373dp3/WiFi-Arduino-Barcode-experimental-/client/Esp8266BarcodeReader/TableViewManager.cpp

// 
// 
// 

#include "TableViewManager.h"


TableViewWrapper::TableViewWrapper(CommonController * pBackController)
{
	char * buf = (char*)malloc(JSON_BUFFER_SIZE * sizeof(char*));
	getList(buf, JSON_BUFFER_SIZE);
	this->parseResponseJson(buf);
	free(buf);

	this->state = CELL_SELECT;
	this->pBackController = pBackController;

	this->dumpSerial();
	this->updateLcd();
}

TableViewWrapper::TableViewWrapper(char * listInfoJson, CommonController * pBackController)
{
	this->parseResponseJson(listInfoJson);

	this->state = CELL_SELECT;
	this->pBackController = pBackController;

	this->dumpSerial();
	this->updateLcd();
}

TableViewWrapper::~TableViewWrapper()
{
	Dispose();
}

void TableViewWrapper::refreshModel()
{
	D("refreshModel");
	Dispose();

	char * buf = (char*)malloc(JSON_BUFFER_SIZE * sizeof(char*));
	getList(buf, JSON_BUFFER_SIZE);
	this->parseResponseJson(buf);
	free(buf);

	this->dumpSerial();
	D("refreshModel . done");
}

void TableViewWrapper::parseResponseJson(const char * json)
{
	D("parseResponseJson");
	char* JsonCharBuffer = (char*)malloc(this->JSON_BUF_LENGTH);
	memset(JsonCharBuffer, 0, this->JSON_BUF_LENGTH);
	JSONBuffer.clear();
	strcpy(JsonCharBuffer, json);
	JsonObject& parsed = JSONBuffer.parseObject(JsonCharBuffer);
	if (parsed.success()) {
		this->pModel = new TableViewModel(&parsed);
	}
	else {
		D("[ERROR] parse failer.");
		Serial.println(json);
	}
	free(JsonCharBuffer);
	D("parseResponseJson . done");
}

void TableViewWrapper::getList(char* buf, int bufsize, int direction, const char* strId)
{
	Serial.println(F("getList"));

	JSONBuffer.clear();
	JsonObject& JSONencoder = JSONBuffer.createObject();
	if (strId != NULL) {
		JSONencoder["id"] = strId;
		D("id: ", strId);
	}
	JSONencoder["name"] = "";
	JSONencoder["mode"] = "list";
	JSONencoder["dir"] = String(direction);

	this->_postCommon(JSONencoder, buf, bufsize);
	HIDSelector::clearBuffer();

	Serial.println(F("getList . done"));
}

void TableViewWrapper::getOtherPage(int8_t direction)
{
	D("pageFlag:", String(pModel->pageFlag).c_str());
	D("direction:", String(direction).c_str());
	//遷移可能なページがない場合は終了
	if (pModel->pageFlag == 0) {
		D("no tr page");
		return;
	}
	//上(新)方向制約
	if ((direction > 0) && ((pModel->pageFlag & 0x01) == 0)) {
		D("no up(new) page");
		return;
	}
	//下(旧)方向制約
	if ((direction < 0) && ((pModel->pageFlag & 0x02) == 0)) {
		D("no down(old) page");
		return;
	}
	String strId = String(this->pModel->ppRows[posY]->strId);

	Dispose();

	char * buf = (char*)malloc(JSON_BUFFER_SIZE * sizeof(char*));
	getList(buf, JSON_BUFFER_SIZE, direction, strId.c_str());
	this->parseResponseJson(buf);
	free(buf);
	strId.~String();

	//フォーカスするセルの検討
	if (direction > 0) {
		//上(新)方向の場合
		lcdPosY = pModel->rowSize - LCD_SIZE_Y;
		posY = pModel->rowSize - 1;
		if (lcdPosY < 0) { lcdPosY = 0; }
		if (posY < 0) { posY = 0; }
		//D("set lcdPosY:", String(lcdPosY).c_str());
		//D("set posY:", String(posY).c_str());
	}
	if (direction < 0) {
		lcdPosY = 0;
		posY = 0;
	}//下(旧)方向の場合

	D("getOtherPage . done");
}

void TableViewWrapper::postUpdate()
{
	//post実行
	JSONBuffer.clear();
	Serial.println(F("postUpdate"));
	JsonObject& JSONencoder = JSONBuffer.createObject();
	JSONencoder["mode"] = "update";
	JSONencoder["id"] = this->pModel->ppRows[posY]->strId;
	JSONencoder["posX"] = posX;

	this->_postCommon(JSONencoder, NULL, 0);

	HIDSelector::clearBuffer();
	Serial.println(F("postUpdate . done"));
}

void TableViewWrapper::postDelete()
{
	JSONBuffer.clear();
	Serial.println(F("postDelete"));
	JsonObject& JSONencoder = JSONBuffer.createObject();
	JSONencoder["mode"] = "delete";
	JSONencoder["id"] = this->pModel->ppRows[posY]->strId;

	this->_postCommon(JSONencoder, NULL, 0);

	HIDSelector::clearBuffer();
}

void TableViewWrapper::_postCommon(JsonObject & JSONencoder, char * responseBuf, int bufsize)
{
	Serial.println(F("_postCommon"));

	//送信処理
	{
		HTTPClient http;
		String url = net.getBaseURL();
		url += net.session_uri;
		Serial.println(url.c_str());
		http.begin(url.c_str());

		JSONencoder["bc"] = HIDSelector::BARCODE;
		JSONencoder["np"] = HIDSelector::TENKEY;
		JSONencoder["bt"] = net.session_key;
		//JSONencoder["name"] = "";

		uint8_t mac0[6];

#ifdef defined(ESP32)
		esp_efuse_mac_get_default(mac0);
#else 
		WiFi.macAddress(mac0);
#endif

		char macstr[16];
		memset(macstr, 0, sizeof(macstr));
		sprintf(macstr, "%02X%02X%02X%02X%02X%02X", mac0[0], mac0[1], mac0[2], mac0[3], mac0[4], mac0[5]);
		JSONencoder["mac"] = macstr;


		char* JsonCharBuffer = (char*)malloc(JSON_POST_BUFFER_SIZE);
		if (JsonCharBuffer == NULL) {
			Serial.println(F("[ERROR] malloc failed"));
		}
		JSONencoder.printTo(JsonCharBuffer, JSON_POST_BUFFER_SIZE);
		JSONencoder.end();

		Serial.print(F("JSON POST:"));
		Serial.println(JsonCharBuffer);

		bool isOk = false;
		bool isAutoFetch = false;

		while (true) {
			int httpCode = http.POST(JsonCharBuffer);
			if (httpCode > 0) { //Check for the returning code
				String payload = http.getString();
				Serial.print(F("httpCode: "));
				Serial.println(httpCode);
				Serial.print(F("payload: "));
				Serial.println(payload);
				JSONBuffer.clear();

				_printPostResponse(payload, responseBuf, bufsize);

				http.end();
				break;//whileループを抜ける
			}
			else {
				if (Serial.available() > 10) { return; }//設定書き込み指示
				Serial.println(F("Error on HTTP request"));
				lcd.clear();
				lcd.setCursor(0, 0);
				lcd.print(F("ERROR 003"));
				lcd.setCursor(0, 1);
				lcd.print(F("CONN failure"));
				delay(3000);
				http.end();
			}

		}
		free(JsonCharBuffer);

	}//送信処理終わり

	Serial.println(F("_postCommon . done"));

}

void TableViewWrapper::_printPostResponse(String & payload, char * responseBuf, int bufsize)
{
	D("_printPostResponse");
	JsonObject& parsed = JSONBuffer.parseObject(payload);
	lcd.clear();
	switch (state)
	{
	case TableViewWrapper::CELL_SELECT:
		D("_printPostResponse . CELL_SELECT");
		if (parsed.success() && parsed.containsKey("d")) {
			if (payload.length() < bufsize) {
				strcpy(responseBuf, payload.c_str());
			}
			else {
				lcd.print("SIZE OVER");
			}
			beepCheck(&parsed);
		}
		else {
			Serial.println("no contains d");
			lcd.print(payload);
		}
		break;
	case TableViewWrapper::VALUE_EDIT:
		break;
	case TableViewWrapper::ROW_DELETE:
		break;
	default:
		break;
	}
	parsed.end();
	D("_printPostResponse . done");
}


void TableViewWrapper::valueChange()
{
	if (state == CELL_SELECT) {
		switch (HIDSelector::TENKEY[0])
		{
		case '8':// up
			posY--;
			if (posY < 0) {
				//サーバ連携のページ送り処理
				posY = 0;
				getOtherPage(1);//上のほうが時間が新しいので、8はプラス
			}
			else {
				lcdPosY = posY;//lcdの1行目に表示する行番号
			}
			break;
		case '2':// down
			posY++;
			if (posY > this->pModel->rowSize - 1) { 
				//サーバ連携のページ送り処理
				posY = this->pModel->rowSize - 1;
				getOtherPage(-1);//下のほうが時間が古い。2はマイナス
			}
			else {
				lcdPosY = posY - 1;//lcdの1行目に表示する行番号
			}
			if (lcdPosY < 0) { lcdPosY = 0; }
			break;
		case '4':// left
			posX--;
			if (posX < 0) { posX = 0; }
			break;
		case '6':// right
			posX++;
			break;
		default:
			break;
		}
		this->updateLcd();


		memset(HIDSelector::TENKEY, 0, sizeof(HIDSelector::TENKEY));
	}

	if (state == VALUE_EDIT) {
		scr.onChangeTenkey(HIDSelector::TENKEY);
	}

	if(state == ROW_DELETE) {
		switch (HIDSelector::TENKEY[0])
		{
		case '1':// ok
			//サーバへの削除コマンド送信
			Serial.print(F("delete ok, posY:"));
			Serial.println(posY);
			D("id:", this->pModel->ppRows[posY]->strId);
			this->postDelete();

			//画面遷移
			posX = 0; posY = 0; lcdPosY = 0;
			state = CELL_SELECT;
			this->refreshModel();
			this->_updateLcdCELL_SELECT();

			break;
		case '9':// Cancel
			Serial.println(F("delete cancel"));
			state = CELL_SELECT;
			this->updateLcd();
			break;
		default:
			break;
		}

		memset(HIDSelector::TENKEY, 0, sizeof(HIDSelector::TENKEY));
	}

}


void TableViewWrapper::onBarcodeEnter()
{
	if (strcmp(HIDSelector::BARCODE, "RB$%") == 0) {
#ifdef DP3_ESP32
#else
		ESP.reset();
#endif
	}
	if (strcmp(HIDSelector::BARCODE, "HO$%") == 0) {
	}
	//EE$% (Edit End)
	if (strcmp(HIDSelector::BARCODE, "EE$%") == 0) {
		HIDSelector::setCommonController(this->pBackController);
		this->pBackController->resume();
	}
}

void TableViewWrapper::onTenkeyEnter()
{
	if (state == VALUE_EDIT) {
		//サーバへの編集コマンド送信
		Serial.print(F("edit pos:"));
		Serial.print(posX);
		Serial.print(F(", "));
		Serial.print(posY);
		Serial.print(F(" => "));
		Serial.println(HIDSelector::TENKEY);
		D("id:", this->pModel->ppRows[posY]->strId);
		this->postUpdate();
		state = CELL_SELECT;
		this->refreshModel();
		//画面遷移
		this->_updateLcdCELL_SELECT();
	}
	else {
		Serial.print("posX:"); Serial.print(posX);
		Serial.print(" colSize:"); Serial.println(pModel->ppRows[0]->colSize);
		//削除を選択しているか？
		if (posX >= pModel->ppRows[0]->colSize) {
			lcd.clear();
			lcd.setCursor(0, 0);
			//ｻｸｼﾞｮ ｼﾏｽｶ?
			lcd.print(F("\xbb\xb8\xbc\xde\xae\x20\xbc\xcf\xbd\xb6\x3f"));
			lcd.setCursor(0, 1);
			lcd.print(F("OK:1 Cancel:9"));
			state = ROW_DELETE;
		}
		else {
			state = VALUE_EDIT;
			this->_updateLcdVALUE_EDIT();
		}
	}
}

void TableViewWrapper::updateLcd()
{
	if (state == CELL_SELECT) {
		this->_updateLcdCELL_SELECT();
	}
	else {
		this->_updateLcdVALUE_EDIT();
	}
}

void TableViewWrapper::_updateLcdCELL_SELECT()
{
	lcd.clear();
	lcd.setCursor(0, 0);
	if (this->pModel == NULL) {
		lcd.print(F("No model"));
		return;
	}
	int rowSize = this->pModel->rowSize;
	if (rowSize == 0) {
		lcd.print(F("Row size: 0"));
		return;
	}
	int colSize = this->pModel->ppRows[0]->colSize;
	if (colSize == 0) {
		lcd.print(F("Col size: 0"));
		return;
	}

	//配列を超えない事の保証(削除付き)
	if (posX > colSize) { posX = colSize; }

	int printLen = 0;

	Serial.print("use lcdPosY:"); Serial.println(lcdPosY);
	Serial.print("use posY:"); Serial.println(posY);

	//時刻部分の描画
	if (posX == 0) {
		for (int i = lcdPosY; i < lcdPosY + LCD_SIZE_Y; i++) {
			if (i >= pModel->rowSize) { break; }
			lcd.setCursor(0, i - lcdPosY);
			char * val = pModel->ppRows[i]->strHhMm;
			lcd.print(val);
			int tmpLen = strlen(val);
			if (printLen < tmpLen) { printLen = tmpLen; }
		}
	}
	printLen += 1;

	//X方向表示原点の調査
	int printLenOrg = printLen;
	int orgX = 0;
	//Serial.println("--");
	//Serial.print("colSize:"); Serial.println(colSize);
	//Serial.print("posX:"); Serial.println(posX);
	for (int i = 0; i < colSize - orgX + 1/* +1は削除分 */; i++) {
		//Serial.print("	i:"); Serial.println(i);
		int maxLen = 0;
		if (i == colSize - orgX) {
			//削除
			maxLen = DELETE_WORD_LENGTH;
			//Serial.println("append delete_word_length into maxLen.");
		}
		else {
			//通常セル
			for (int j = 0; j < rowSize; j++) {
				int tmpLen = strlen(pModel->ppRows[j]->ppCols[i + orgX]);
				if (maxLen < tmpLen) { maxLen = tmpLen; }
			}
		}
		printLen += maxLen + 1;
		//超過した場合は、原点を1オフセットして再計算
		//(初回から超過する場合は除外)
		Serial.print("	printLen:"); Serial.println(printLen);
		if ((printLen >= LCD_SIZE_X) && (i > 0)) {
			i = -1;
			printLen = printLenOrg;
			orgX++;
			//Serial.print("size over. inc offset: "); Serial.println(orgX);
		}
		//超過せずにたどり着いた場合は終了
		if (i + orgX == posX) {
			//Serial.println("Break");
			break;
		}
	}
	//Serial.print("orgX: "); Serial.println(orgX);
	printLen = printLenOrg;


	//配列部分の描画
	for (int i = orgX; i < colSize + 1; i++) {
		int maxLen = 0;
		if (i >= colSize) {
			for (int j = 0; j < rowSize; j++) {
				//ｻｸｼﾞｮ
				int tmpLen = DELETE_WORD_LENGTH;//半角カナ5文字
				if (maxLen < tmpLen) { maxLen = tmpLen; }
				//表示範囲外のデータはLCDにコマンドを送らない
				if (j < lcdPosY) { continue; }
				if (j >= lcdPosY + LCD_SIZE_Y) { continue; }
				lcd.setCursor(printLen, j - lcdPosY);
				lcd.print(F("\xbb\xb8\xbc\xde\xae"));
			}
		}
		else {
			for (int j = 0; j < rowSize; j++) {
				char* val = pModel->ppRows[j]->ppCols[i];
				int tmpLen = strlen(val);
				if (maxLen < tmpLen) { maxLen = tmpLen; }
				//表示範囲外のデータはLCDにコマンドを送らない
				if (j < lcdPosY) { continue; }
				if (j >= lcdPosY + LCD_SIZE_Y) { continue; }
				lcd.setCursor(printLen, j - lcdPosY);
				lcd.print(val);
			}
		}

		//カーソルの描画判定
		if (i == posX) {
			lcd.setCursor(printLen - 1, posY - lcdPosY);
			lcd.print("[");
			lcd.setCursor(printLen + maxLen, posY - lcdPosY);
			lcd.print("]");
		}
		printLen += maxLen + 1;

		//表示範囲を超えている場合は'>'で埋める
		if ((printLen >= LCD_SIZE_X) && (i != posX)) {
			char* tmpChar = (char*)malloc(maxLen + 1);
			for (int i = 0; i < maxLen; i++) tmpChar[i] = '>';
			tmpChar[maxLen] = 0x00;
			lcd.setCursor(printLen - maxLen - 1, 0);
			lcd.print(tmpChar);
			if (pModel->rowSize > 1) {
				lcd.setCursor(printLen - maxLen - 1, 1);
			}
			lcd.print(tmpChar);
			free(tmpChar);
			break;
		}
	}
	//*/

}

void TableViewWrapper::_updateLcdVALUE_EDIT()
{
	lcd.clear();
	lcd.setCursor(0, 0);
	lcd.print(F("EDIT: "));
	lcd.print(this->pModel->ppRows[posY]->ppCols[posX]);
}


TableViewWrapper::TableViewModel::TableViewModel(JsonObject * jsonObj)
{
	if (jsonObj == NULL) return;
	JsonObject& json = (*jsonObj);
	if (json.containsKey("d")) {
		JsonArray& ary = json["d"].asArray();
		int size = ary.size();
		this->rowSize = size;
		this->ppRows = (TableViewRowModel**)malloc(size * sizeof(TableViewRowModel**));
		for (int i = 0; i < size; i++) {
			TableViewRowModel *row = new TableViewRowModel(&(ary[i].asObject()));
			this->ppRows[i] = row;
		}
	}
	if (json.containsKey("pflg")) {
		int tmpFlg = atol(json["pflg"].asString());
		if ((tmpFlg >= 0) && (tmpFlg <= 3)) {
			this->pageFlag = tmpFlg;
		}
		else {
			this->pageFlag = 0;
		}
	}
}

void TableViewWrapper::TableViewModel::dumpSerial()
{
	D("rowSize", String(this->rowSize).c_str());
	for (int i = 0; i < rowSize; i++) {
		this->ppRows[i]->dumpSerial();
	}
}

TableViewWrapper::TableViewRowModel::TableViewRowModel(JsonObject * jsonObj)
{
	if (jsonObj == NULL) return;
	JsonObject& json = (*jsonObj);
	if (json.containsKey("id")) {
		copyChar(&this->strId, json["id"].asString());
	}
	if (json.containsKey(F("hhmm"))) {
		copyChar(&this->strHhMm, json["hhmm"].asString());
	}
	if (json.containsKey("cols")) {
		JsonArray& ary = json["cols"].asArray();
		int size = ary.size();
		this->colSize = size;
		this->ppCols = (char**)malloc(size * sizeof(char**));
		for (int i = 0; i < size; i++) {
			copyChar(&(ppCols[i]), ary[i].asString());
		}
	}
}

void TableViewWrapper::TableViewRowModel::dumpSerial()
{
	D("id", this->strId, 1);
	D("hhmm", this->strHhMm, 1);
	D("colSize", String(this->colSize).c_str(), 1);

	Serial.print(F("    "));
	for (int i = 0; i < colSize; i++) {
		Serial.print(ppCols[i]);
		if (i == colSize - 1) {
			Serial.println();
			break;
		}
		Serial.print(", ");
	}
}
